Krishnawa/BEEWATCH/Datasheet/Switch/1883783.jpg

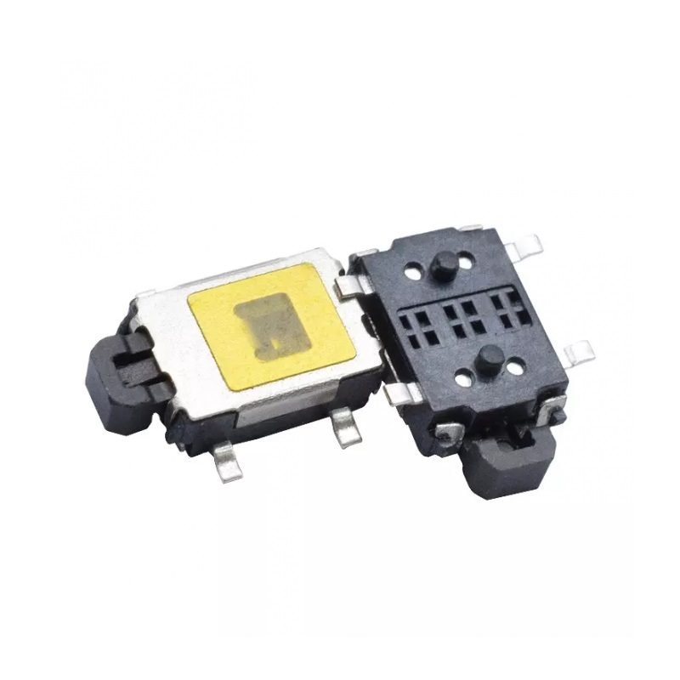
Datasheet/Switch/1883783.jpg
