Krishnawa/BEEWATCH/Arduino/Gyro/MPU6050_test_code/MPU6050_test_code.ino

#include <Wire.h>
#include <Adafruit_MPU6050.h>
#include <Adafruit_Sensor.h>

Adafruit_MPU6050 mpu;

void setup() {
  Serial.begin(115200);
  Wire.begin(3, 4);  // SDA = GPIO3, SCL = GPIO4

  if (!mpu.begin(0x68, &Wire)) {
    Serial.println("Failed to find MPU6050 chip");
    while (1) {
      delay(10);
    }
  }

  Serial.println("MPU6050 Found!");
  mpu.setAccelerometerRange(MPU6050_RANGE_8_G);
  mpu.setGyroRange(MPU6050_RANGE_500_DEG);
  mpu.setFilterBandwidth(MPU6050_BAND_21_HZ);
  delay(100);
}

void loop() {
  sensors_event_t a, g, temp;
  mpu.getEvent(&a, &g, &temp);

  Serial.print("Accel X: "); Serial.print(a.acceleration.x);
  Serial.print(", Y: "); Serial.print(a.acceleration.y);
  Serial.print(", Z: "); Serial.println(a.acceleration.z);

  Serial.print("Gyro X: "); Serial.print(g.gyro.x);
  Serial.print(", Y: "); Serial.print(g.gyro.y);
  Serial.print(", Z: "); Serial.println(g.gyro.z);

  Serial.print("Temp: "); Serial.print(temp.temperature);
  Serial.println(" degC");

  Serial.println("");
  delay(1000);
}
